ChladpavPy/DIY-marauder/Images/3d_case2.png

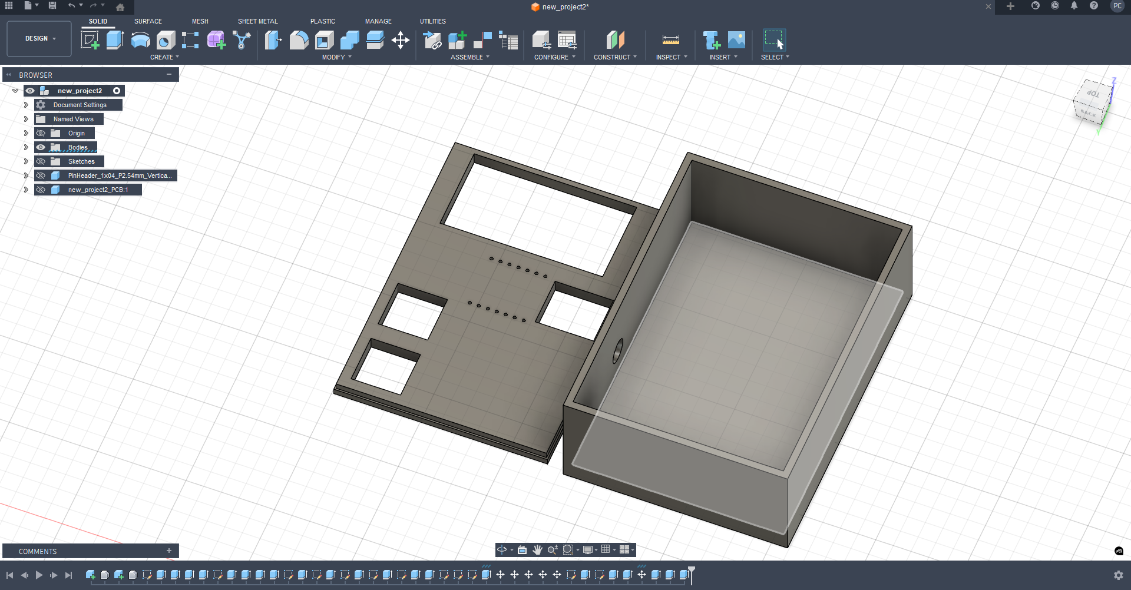
Images/3d_case2.png
