ChladpavPy/DIY-marauder/Images/3d_case_with_pcb.png

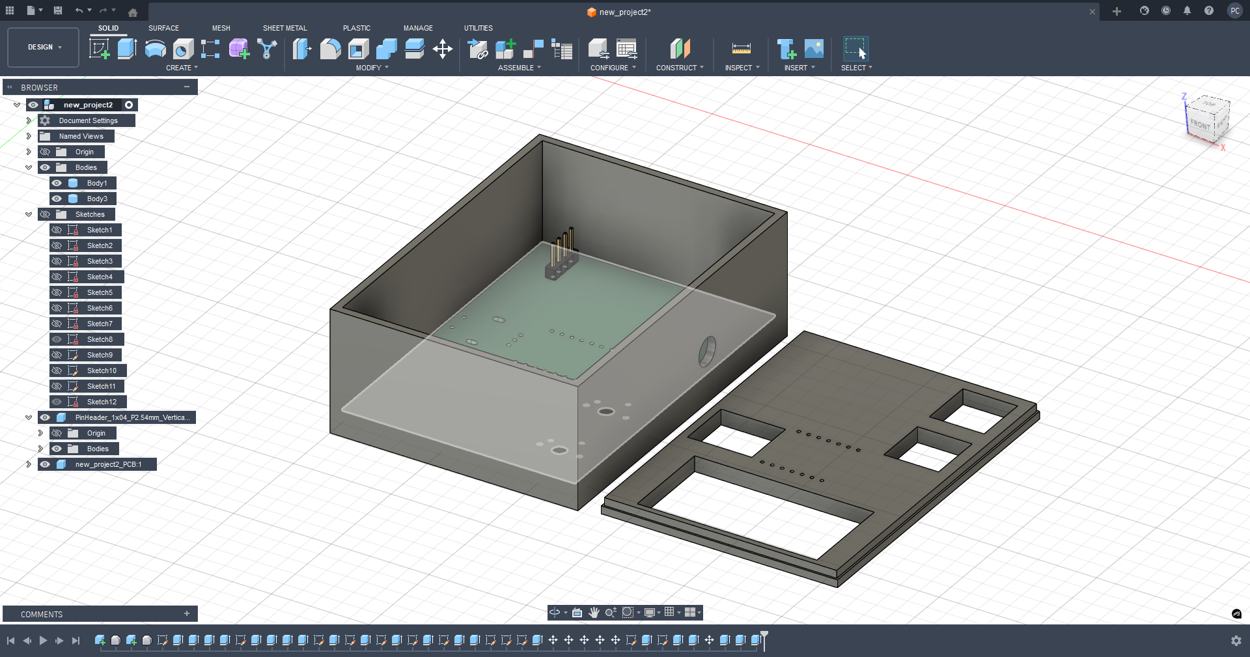
Images/3d_case_with_pcb.png
