ChladpavPy/DIY-marauder/Images/full_3d_case2.png

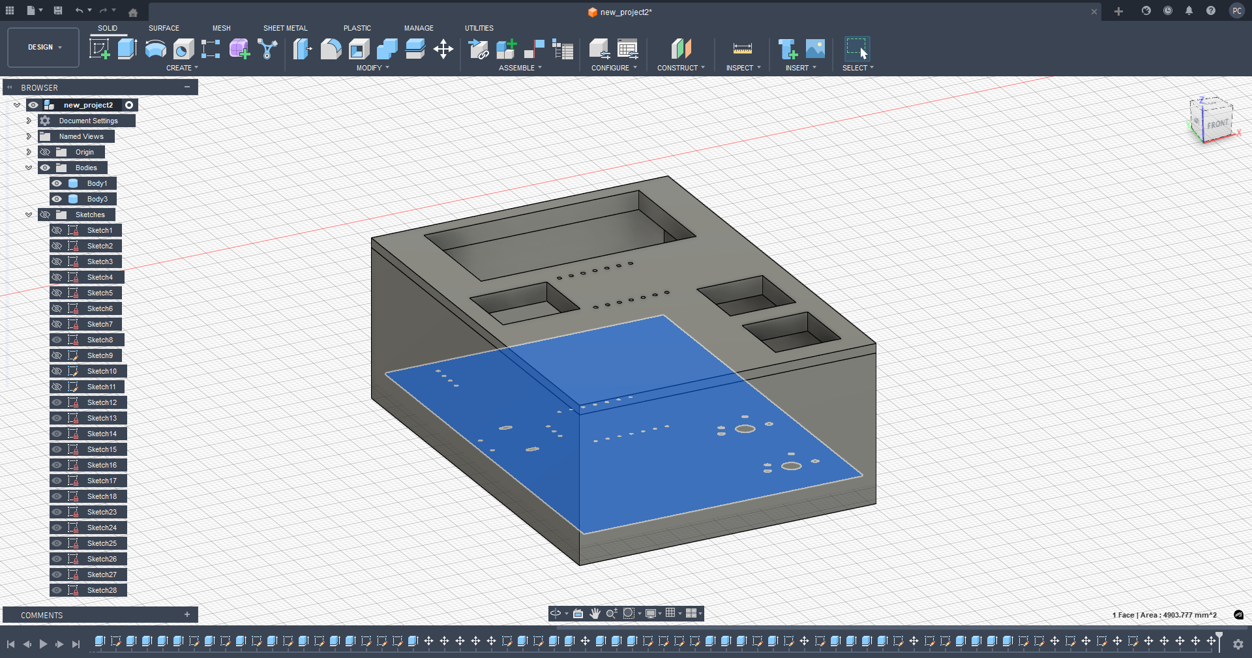
Images/full_3d_case2.png
