ChladpavPy/DIY-marauder/Images/model2.png

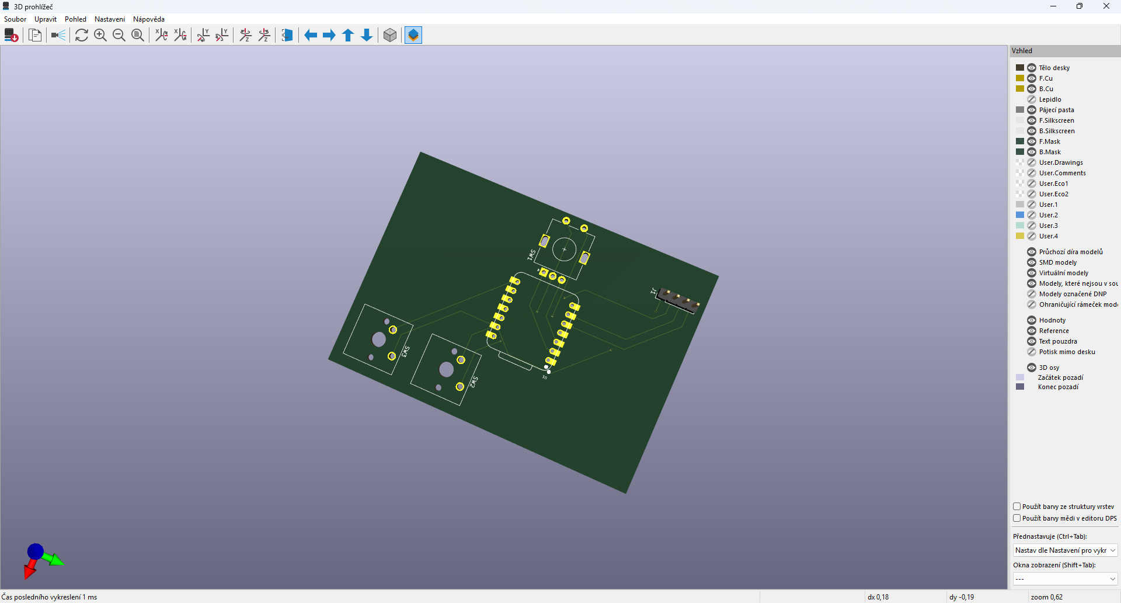
Images/model2.png
