ChladpavPy/DIY-marauder/Images/model3.png

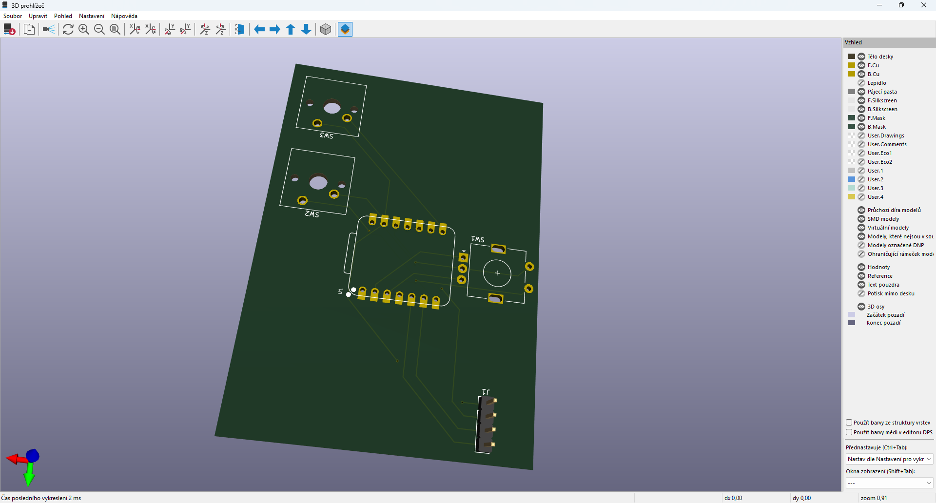
Images/model3.png
