ChladpavPy/DIY-marauder/Images/transparent_case2.png

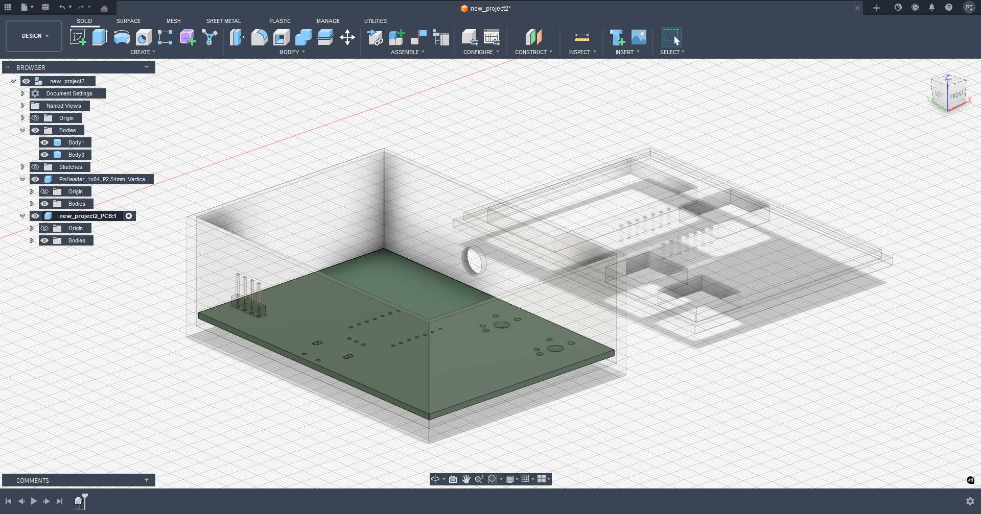
Images/transparent_case2.png
