ChladpavPy/DIY-marauder/Images/transparent_case3.png

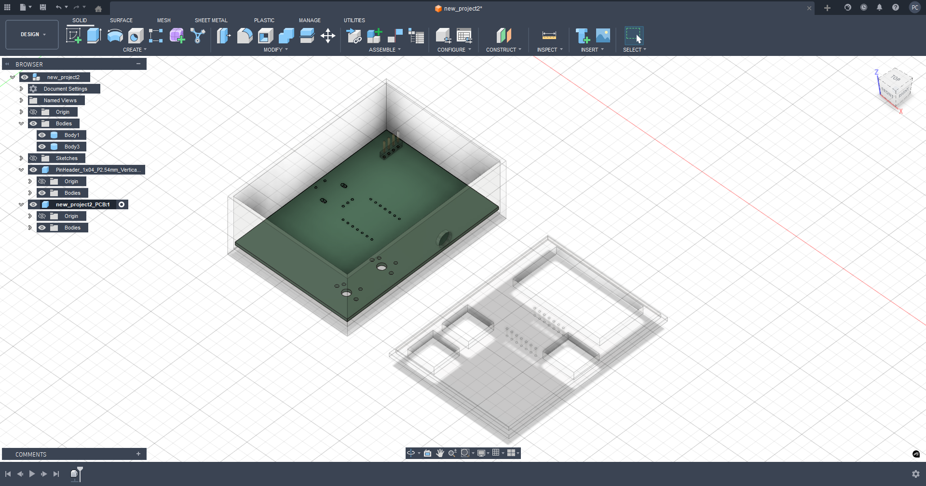
Images/transparent_case3.png
